RAnders00/usbc-fursuit-fan/fursuit-fan-controller-fw/src/lib.rs

#![no_main]
#![no_std]

pub mod persistence;
pub mod task;

use defmt_rtt as _; // global logger

use embassy_stm32 as _; // memory layout

use panic_probe as _;

// same panicking *behavior* as `panic-probe` but doesn't print a panic message
// this prevents the panic message being printed *twice* when `defmt::panic` is invoked
#[defmt::panic_handler]
fn panic() -> ! {
    cortex_m::asm::udf()
}

/// Terminates the application and makes a semihosting-capable debug tool exit
/// with status code 0.
pub fn exit() -> ! {
    semihosting::process::exit(0);
}

/// Hardfault handler.
///
/// Terminates the application and makes a semihosting-capable debug tool exit
/// with an error. This seems better than the default, which is to spin in a
/// loop.
#[cortex_m_rt::exception]
unsafe fn HardFault(_frame: &cortex_m_rt::ExceptionFrame) -> ! {
    semihosting::process::exit(1);
}
